vineethk96/ultrasonic_anemometer/CAD/Exhibit/baseBox.dxf

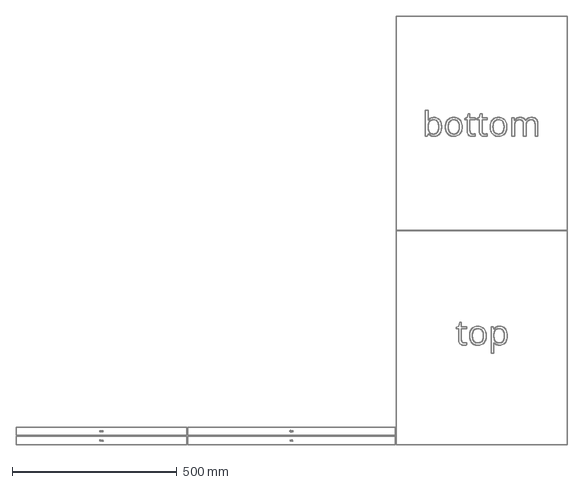
[picture p17: CAD file, 2025-07-08]
CAD/Exhibit/baseBox.dxf
1672.0 x 1299.0 mm
