vineethk96/ultrasonic_anemometer/CAD/Exhibit/Spur Gear 36 Teeth - Spur Gear.stl

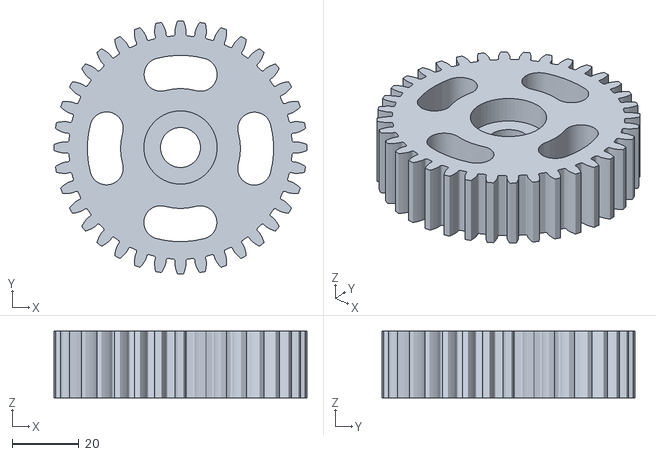
[picture p18: CAD file, 2025-07-07]
CAD/Exhibit/Spur Gear 36 Teeth - Spur Gear.stl
76.0 x 76.0 x 20.0
