vineethk96/ultrasonic_anemometer/CAD/Exhibit/building.dxf

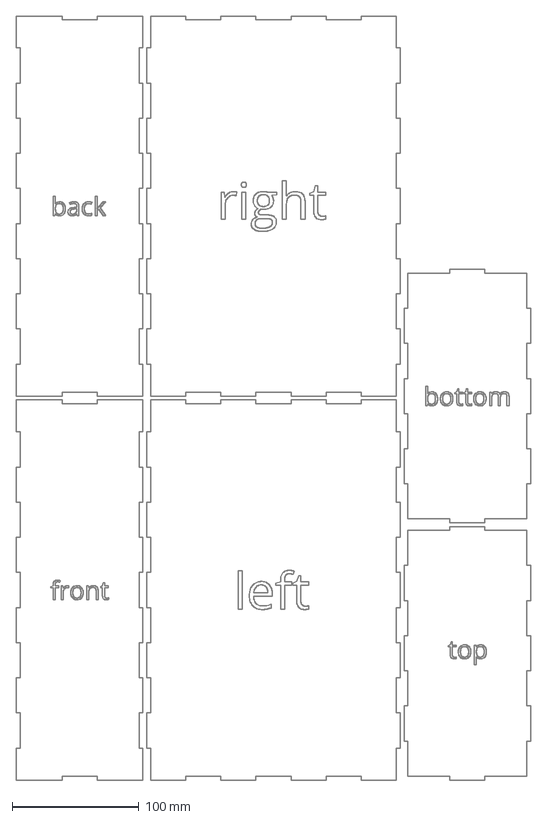
[picture p19: CAD file, 2025-07-07]
CAD/Exhibit/building.dxf
406.0 x 603.0 mm
