vineethk96/ultrasonic_anemometer/CAD/Exhibit/Upper Rack.stl

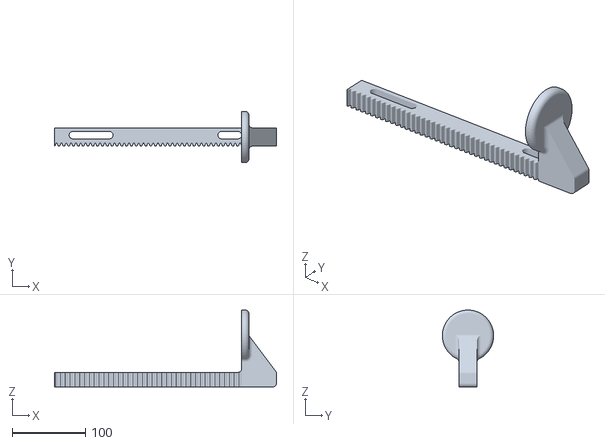
[picture p20: CAD file, 2025-07-07, an earlier design]
CAD/Exhibit/Upper Rack.stl
303.0 x 69.9 x 105.0
