vineethk96/ultrasonic_anemometer/data_collector/initialTest/hanaFan_open_noTrees.csv

timestamp | topic | wind_speed | wind_direction
2025-08-05T17:10:56.705653 | student/ultrasonic_anemometer | 3.8 | 130.0
2025-08-05T17:10:57.774324 | student/ultrasonic_anemometer | 3.79 | 130.0
2025-08-05T17:10:58.711314 | student/ultrasonic_anemometer | 3.85 | 131.0
2025-08-05T17:10:59.719029 | student/ultrasonic_anemometer | 3.92 | 132.0
2025-08-05T17:11:00.716467 | student/ultrasonic_anemometer | 3.92 | 132.0
2025-08-05T17:11:01.718943 | student/ultrasonic_anemometer | 3.91 | 132.0
2025-08-05T17:11:02.724425 | student/ultrasonic_anemometer | 3.92 | 132.0
2025-08-05T17:11:03.728461 | student/ultrasonic_anemometer | 3.91 | 133.0
2025-08-05T17:11:04.732485 | student/ultrasonic_anemometer | 3.85 | 132.0
2025-08-05T17:11:05.731761 | student/ultrasonic_anemometer | 3.81 | 132.0
2025-08-05T17:11:06.734589 | student/ultrasonic_anemometer | 3.86 | 132.0
2025-08-05T17:11:07.743644 | student/ultrasonic_anemometer | 3.9 | 133.0
2025-08-05T17:11:08.740354 | student/ultrasonic_anemometer | 3.83 | 132.0
2025-08-05T17:11:09.745873 | student/ultrasonic_anemometer | 3.78 | 131.0
2025-08-05T17:11:10.746693 | student/ultrasonic_anemometer | 3.79 | 131.0
2025-08-05T17:11:11.750566 | student/ultrasonic_anemometer | 3.79 | 131.0
2025-08-05T17:11:12.751751 | student/ultrasonic_anemometer | 3.84 | 132.0
2025-08-05T17:11:13.758151 | student/ultrasonic_anemometer | 3.83 | 131.0
2025-08-05T17:11:14.760153 | student/ultrasonic_anemometer | 3.86 | 132.0
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
2025-08-05T17:14:12.292103 | student/ultrasonic_anemometer | 3.78 | 132.0
2025-08-05T17:14:13.294719 | student/ultrasonic_anemometer | 3.74 | 132.0
2025-08-05T17:14:14.297665 | student/ultrasonic_anemometer | 3.75 | 132.0
2025-08-05T17:14:15.300761 | student/ultrasonic_anemometer | 3.78 | 133.0
2025-08-05T17:14:16.303506 | student/ultrasonic_anemometer | 3.8 | 133.0
