vineethk96/ultrasonic_anemometer/data_collector/initialTest/hanaFan_open_treeStrip.csv

timestamp | topic | wind_speed | wind_direction
2025-08-05T17:19:01.162500 | student/ultrasonic_anemometer | 3.61 | 134.0
2025-08-05T17:19:02.166653 | student/ultrasonic_anemometer | 3.64 | 135.0
2025-08-05T17:19:03.169138 | student/ultrasonic_anemometer | 3.62 | 134.0
2025-08-05T17:19:04.174667 | student/ultrasonic_anemometer | 3.61 | 134.0
2025-08-05T17:19:05.175551 | student/ultrasonic_anemometer | 3.59 | 133.0
2025-08-05T17:19:06.178260 | student/ultrasonic_anemometer | 3.59 | 133.0
2025-08-05T17:19:07.184466 | student/ultrasonic_anemometer | 3.59 | 132.0
2025-08-05T17:19:08.184856 | student/ultrasonic_anemometer | 3.61 | 132.0
2025-08-05T17:19:09.188748 | student/ultrasonic_anemometer | 3.68 | 133.0
2025-08-05T17:19:10.190102 | student/ultrasonic_anemometer | 3.66 | 132.0
2025-08-05T17:19:11.193738 | student/ultrasonic_anemometer | 3.68 | 133.0
2025-08-05T17:19:12.196897 | student/ultrasonic_anemometer | 3.66 | 133.0
2025-08-05T17:19:13.198942 | student/ultrasonic_anemometer | 3.71 | 134.0
2025-08-05T17:19:14.202464 | student/ultrasonic_anemometer | 3.76 | 134.0
2025-08-05T17:19:15.205117 | student/ultrasonic_anemometer | 3.81 | 135.0
2025-08-05T17:19:16.208362 | student/ultrasonic_anemometer | 3.84 | 136.0
2025-08-05T17:19:17.210919 | student/ultrasonic_anemometer | 3.88 | 136.0
2025-08-05T17:19:18.213738 | student/ultrasonic_anemometer | 3.9 | 136.0
2025-08-05T17:19:19.217873 | student/ultrasonic_anemometer | 3.84 | 136.0
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
2025-08-05T17:22:16.757958 | student/ultrasonic_anemometer | 3.45 | 135.0
2025-08-05T17:22:17.762837 | student/ultrasonic_anemometer | 3.41 | 135.0
2025-08-05T17:22:18.762043 | student/ultrasonic_anemometer | 3.36 | 134.0
2025-08-05T17:22:19.765496 | student/ultrasonic_anemometer | 3.29 | 134.0
2025-08-05T17:22:20.768329 | student/ultrasonic_anemometer | 3.24 | 134.0
