vineethk96/ultrasonic_anemometer/data_collector/initialTest/hanaFan_open_trees.csv

timestamp | topic | wind_speed | wind_direction
2025-08-05T17:23:42.016314 | student/ultrasonic_anemometer | 2.41 | 141.0
2025-08-05T17:23:43.019755 | student/ultrasonic_anemometer | 2.32 | 141.0
2025-08-05T17:23:44.021261 | student/ultrasonic_anemometer | 2.37 | 142.0
2025-08-05T17:23:45.027914 | student/ultrasonic_anemometer | 2.49 | 141.0
2025-08-05T17:23:46.028344 | student/ultrasonic_anemometer | 2.65 | 139.0
2025-08-05T17:23:47.030636 | student/ultrasonic_anemometer | 2.84 | 139.0
2025-08-05T17:23:48.033984 | student/ultrasonic_anemometer | 3.07 | 138.0
2025-08-05T17:23:49.036835 | student/ultrasonic_anemometer | 3.19 | 137.0
2025-08-05T17:23:50.039679 | student/ultrasonic_anemometer | 3.34 | 137.0
2025-08-05T17:23:51.042683 | student/ultrasonic_anemometer | 3.44 | 135.0
2025-08-05T17:23:52.048091 | student/ultrasonic_anemometer | 3.54 | 135.0
2025-08-05T17:23:53.048504 | student/ultrasonic_anemometer | 3.68 | 134.0
2025-08-05T17:23:54.051207 | student/ultrasonic_anemometer | 3.83 | 134.0
2025-08-05T17:23:55.054250 | student/ultrasonic_anemometer | 3.89 | 134.0
2025-08-05T17:23:56.059569 | student/ultrasonic_anemometer | 3.93 | 134.0
2025-08-05T17:23:57.062738 | student/ultrasonic_anemometer | 3.93 | 134.0
2025-08-05T17:23:58.063359 | student/ultrasonic_anemometer | 3.94 | 134.0
2025-08-05T17:23:59.066577 | student/ultrasonic_anemometer | 3.97 | 134.0
2025-08-05T17:24:00.069582 | student/ultrasonic_anemometer | 3.97 | 134.0
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
2025-08-05T17:26:57.611011 | student/ultrasonic_anemometer | 3.81 | 130.0
2025-08-05T17:26:58.613176 | student/ultrasonic_anemometer | 3.81 | 131.0
2025-08-05T17:26:59.616689 | student/ultrasonic_anemometer | 3.8 | 130.0
2025-08-05T17:27:00.619355 | student/ultrasonic_anemometer | 3.78 | 130.0
2025-08-05T17:27:01.622609 | student/ultrasonic_anemometer | 3.77 | 130.0
