vineethk96/ultrasonic_anemometer/data_collector/initialTest/hana_fan_no_tree.csv

timestamp | topic | wind_speed | wind_direction
2025-08-05T16:43:34.756439 | student/ultrasonic_anemometer | 5.88 | 120.0
2025-08-05T16:43:35.752111 | student/ultrasonic_anemometer | 5.89 | 120.0
2025-08-05T16:43:36.755644 | student/ultrasonic_anemometer | 5.9 | 120.0
2025-08-05T16:43:37.758584 | student/ultrasonic_anemometer | 5.9 | 120.0
2025-08-05T16:43:38.761015 | student/ultrasonic_anemometer | 5.92 | 120.0
2025-08-05T16:43:39.765360 | student/ultrasonic_anemometer | 5.96 | 120.0
2025-08-05T16:43:40.774310 | student/ultrasonic_anemometer | 5.98 | 121.0
2025-08-05T16:43:41.770436 | student/ultrasonic_anemometer | 6.03 | 121.0
2025-08-05T16:43:42.773193 | student/ultrasonic_anemometer | 6.07 | 122.0
2025-08-05T16:43:43.775979 | student/ultrasonic_anemometer | 6.06 | 121.0
2025-08-05T16:43:44.779051 | student/ultrasonic_anemometer | 6.06 | 121.0
2025-08-05T16:43:45.781871 | student/ultrasonic_anemometer | 6.04 | 121.0
2025-08-05T16:43:46.785059 | student/ultrasonic_anemometer | 6.05 | 121.0
2025-08-05T16:43:47.788321 | student/ultrasonic_anemometer | 6.06 | 121.0
2025-08-05T16:43:48.792469 | student/ultrasonic_anemometer | 6.04 | 121.0
2025-08-05T16:43:49.802729 | student/ultrasonic_anemometer | 6.02 | 121.0
2025-08-05T16:43:50.827113 | student/ultrasonic_anemometer | 6.0 | 121.0
2025-08-05T16:43:51.800132 | student/ultrasonic_anemometer | 5.98 | 120.0
2025-08-05T16:43:52.803337 | student/ultrasonic_anemometer | 5.94 | 120.0
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
2025-08-05T16:46:50.340327 | student/ultrasonic_anemometer | 6.04 | 121.0
2025-08-05T16:46:51.343219 | student/ultrasonic_anemometer | 6.02 | 121.0
2025-08-05T16:46:52.346277 | student/ultrasonic_anemometer | 6.04 | 121.0
2025-08-05T16:46:53.349317 | student/ultrasonic_anemometer | 5.99 | 121.0
2025-08-05T16:46:54.357331 | student/ultrasonic_anemometer | 6.0 | 121.0
